HandLeVR/lackierpistole/Druckdateien/Träger/träger.step

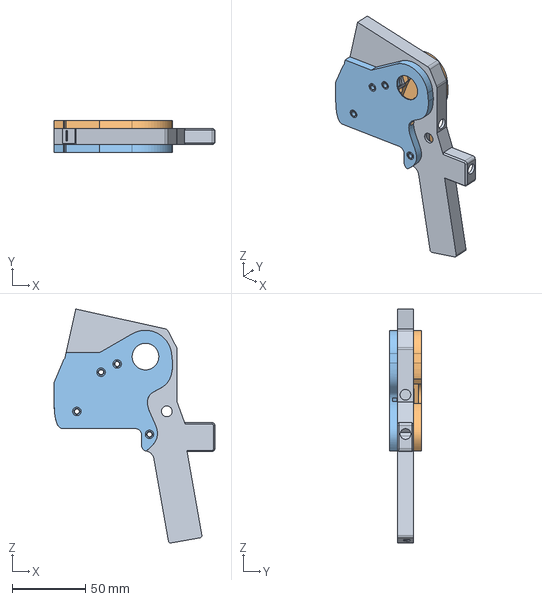
[picture p18: CAD file, 2021-12-02]
Druckdateien/Träger/träger.step
109.6 x 22.0 x 159.5 mm
