HandLeVR/lackierpistole/Druckdateien/Gehäuse/Nase.3mf

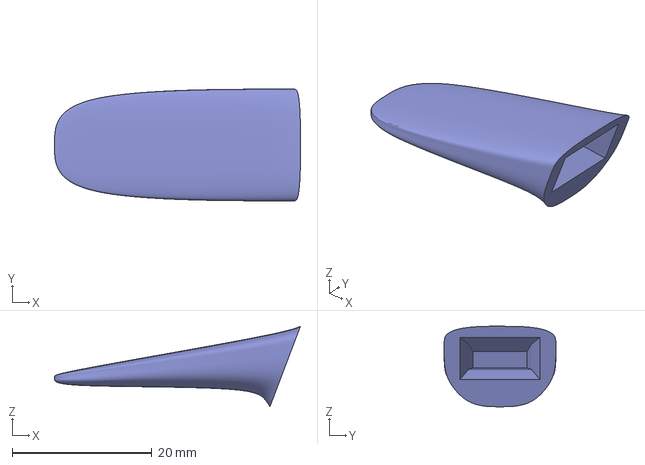
[picture p19: CAD file, 2021-12-02]
Druckdateien/Gehäuse/Nase.3mf
35.2 x 16.0 x 11.5 mm
