HandLeVR/lackierpistole/Druckdateien/Mechanik/Abzug v3.step

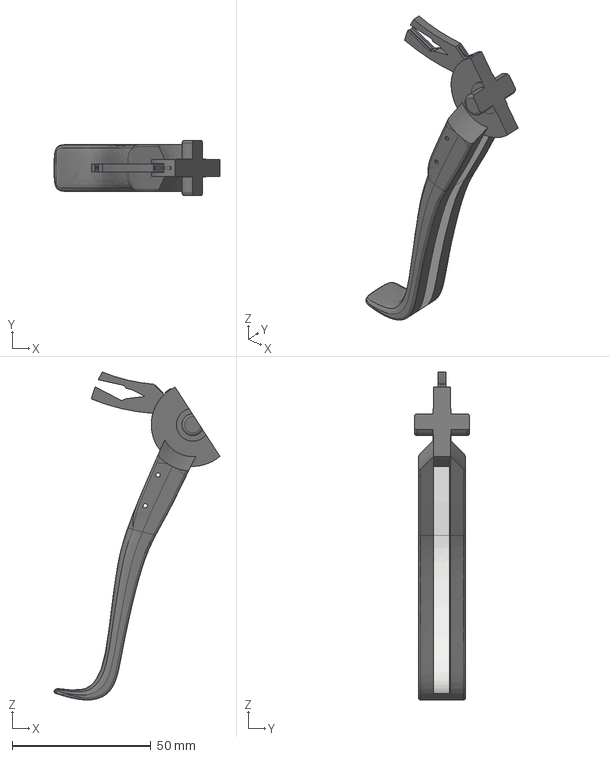
[picture p20: CAD file, 2021-12-02]
Druckdateien/Mechanik/Abzug v3.step
59.8 x 20.0 x 118.2 mm
