HandLeVR/lackierpistole/Druckdateien/Regler/Regler_HiUn.step

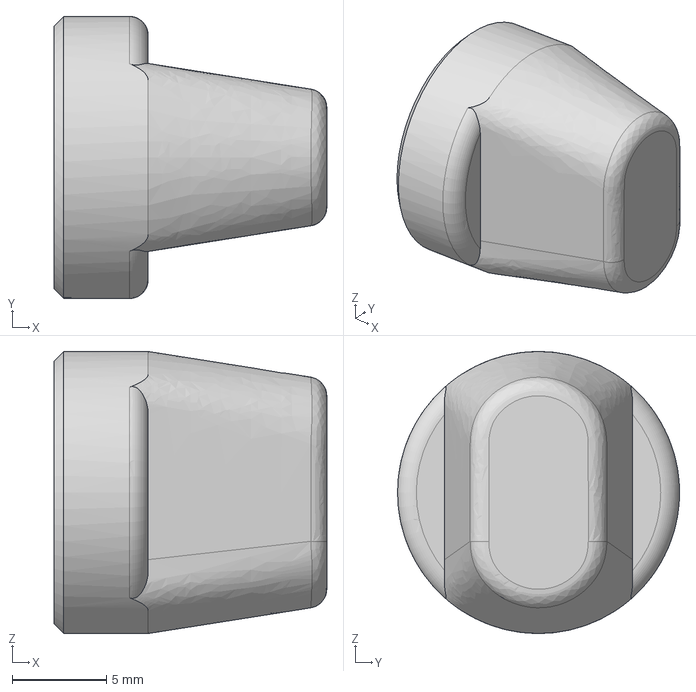
[picture p21: CAD file, 2021-12-02]
Druckdateien/Regler/Regler_HiUn.step
14.5 x 15.0 x 15.0 mm
