HandLeVR/lackierpistole/Druckdateien/Aufnahme/Auflageplatte.3mf

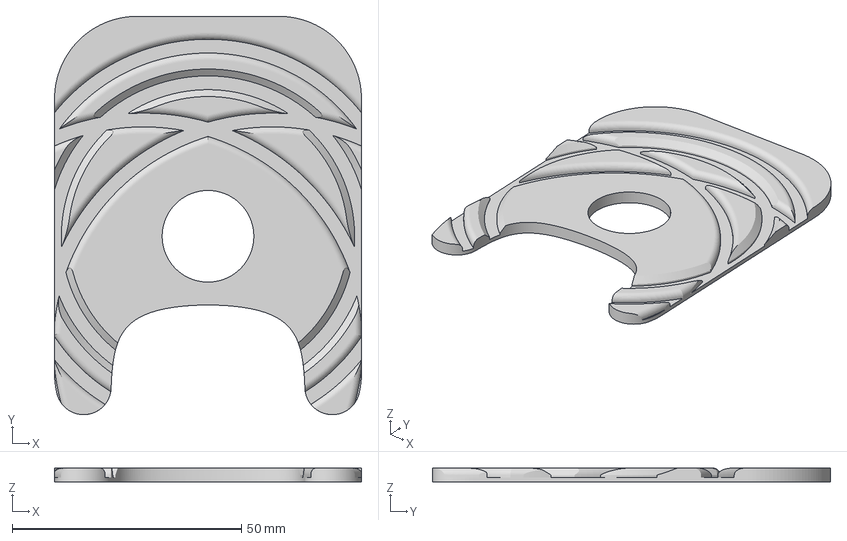
[picture p22: CAD file, 2021-12-02]
Druckdateien/Aufnahme/Auflageplatte.3mf
67.0 x 86.9 x 3.00 mm
