HandLeVR/lackierpistole/Druckdateien/Gehäuse/Nasenzapfen.3mf

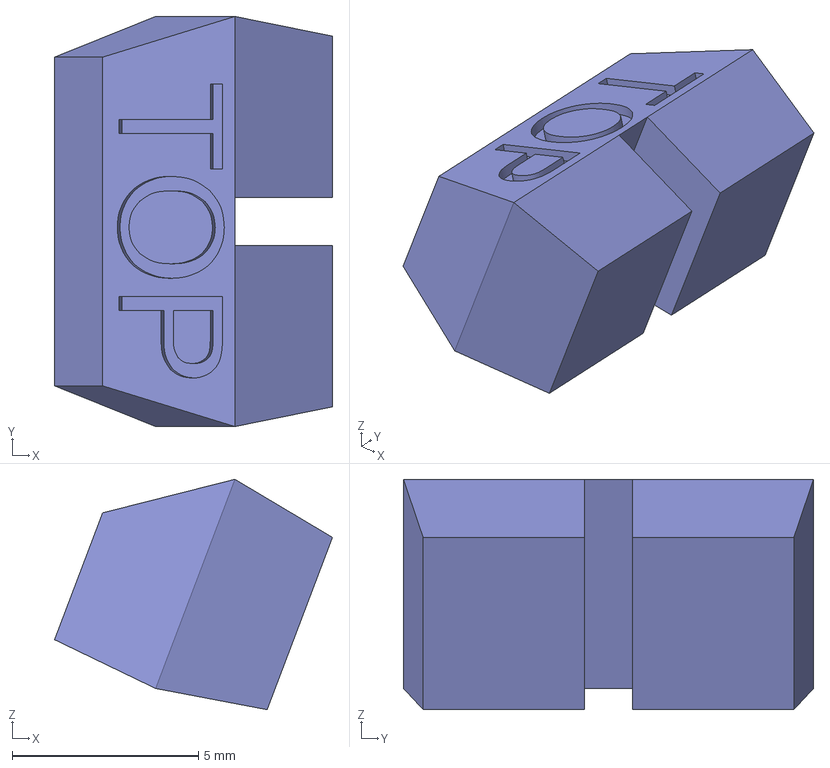
[picture p23: CAD file, 2021-12-02]
Druckdateien/Gehäuse/Nasenzapfen.3mf
7.46 x 11.0 x 6.18 mm
