HandLeVR/lackierpistole/Druckdateien/Mechanik/federhülse.step

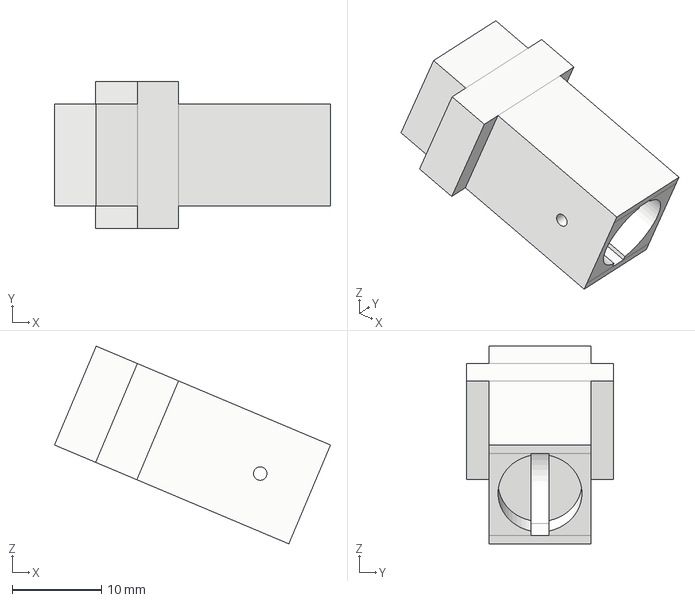
[picture p24: CAD file, 2021-12-02]
Druckdateien/Mechanik/federhülse.step
30.9 x 16.4 x 22.1 mm
