HandLeVR/lackierpistole/Druckdateien/Aufnahme/Schraube.step

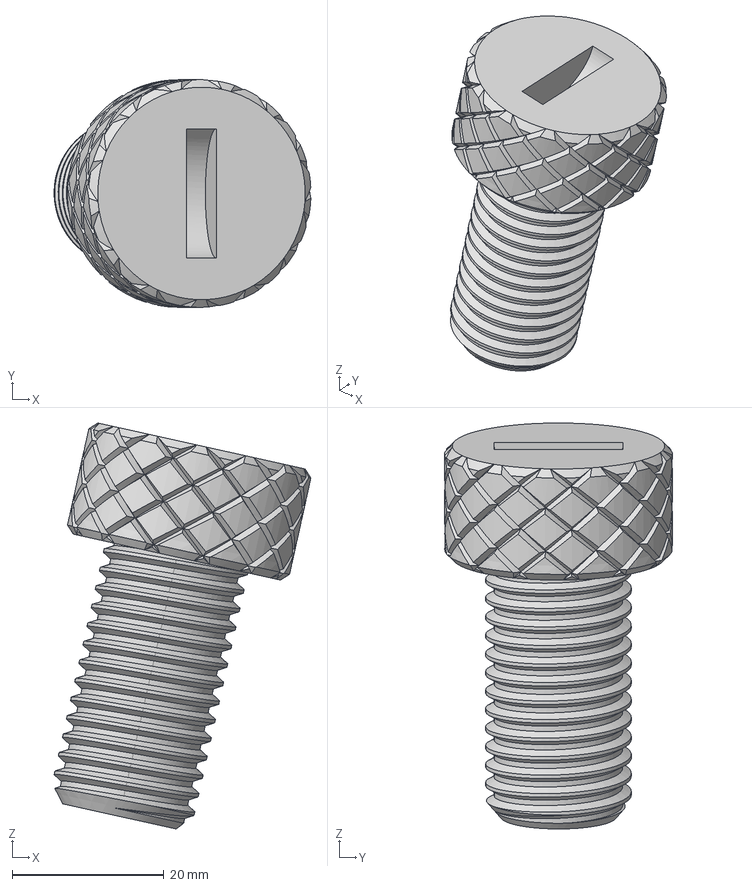
[picture p25: CAD file, 2021-12-02]
Druckdateien/Aufnahme/Schraube.step
33.8 x 30.0 x 53.5 mm
