HandLeVR/lackierpistole/Druckdateien/Gehäuse/gehäuse unten.step

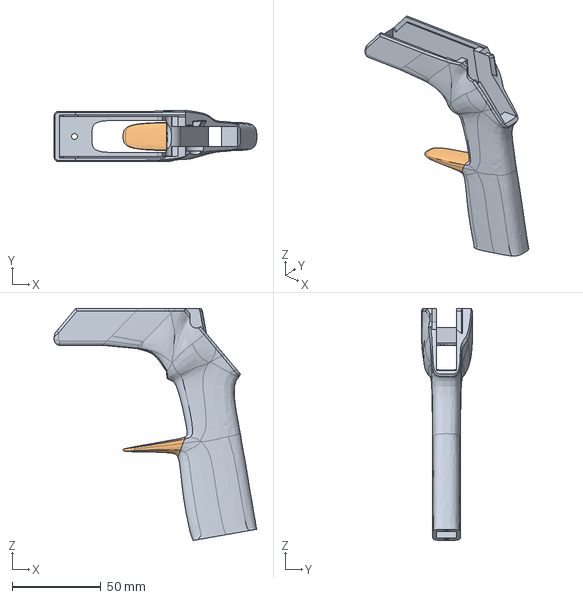
[picture p26: CAD file, 2021-12-02]
Druckdateien/Gehäuse/gehäuse unten.step
114.4 x 29.1 x 131.0 mm
