HandLeVR/lackierpistole/Druckdateien/Aufnahme/klemme v5.step

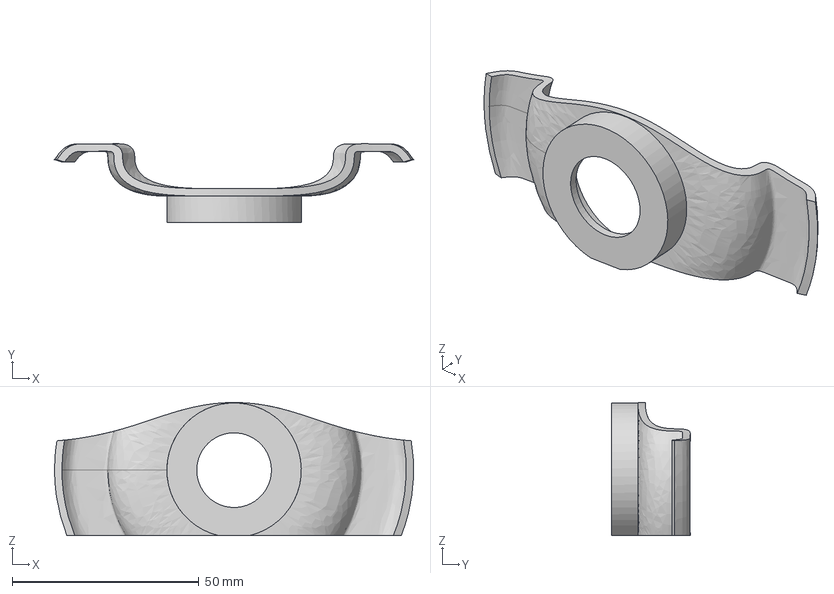
[picture p27: CAD file, 2021-12-02]
Druckdateien/Aufnahme/klemme v5.step
96.1 x 21.1 x 35.6 mm
